luisgongod/ESD_Modular/model_14/software/calibration_values_m14.py

#only 5 volts:
INPUT_CALIBRATION_VALUES=[65139,58626,52114,45601,39089,32576,26063,19551,13038,6526,13]
INPUT_CALIBRATION_VALUES=[65139,13]
INPUT_CALIBRATION_VALUES_2=[65139,13]
INPUT_CALIBRATION_VALUES_3=[65139,13]
INPUT_CALIBRATION_VALUES_4=[65139,13]


OUTPUT_CALIBRATION_VALUES=[0, 7800, 14000, 20100, 26300, 32400, 38400, 44600, 50600, 56800, 65600]
